open-ephys/onix-breakout/mechanical/case/components/cherryMX/Renderings/untitled.199.jpg

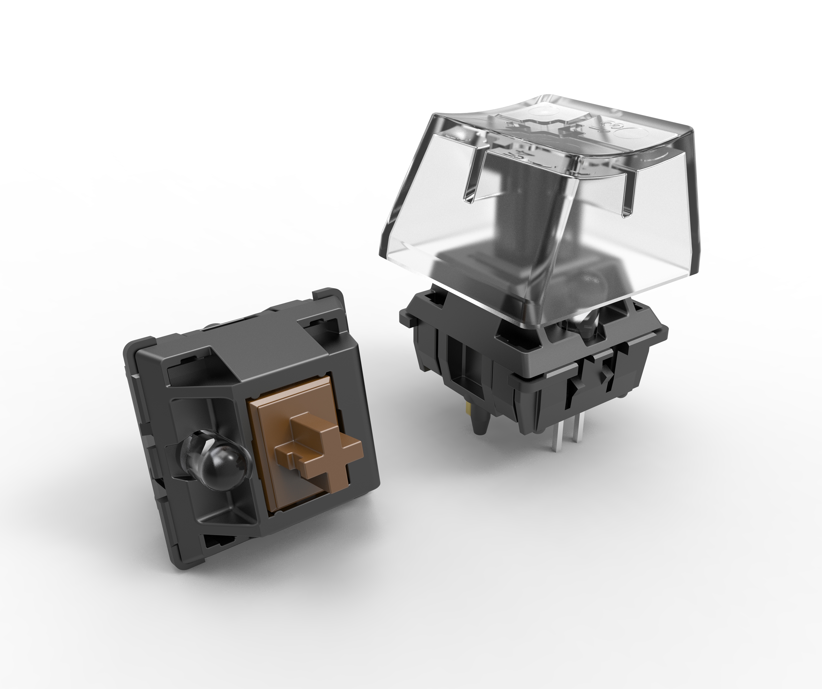
mechanical/case/components/cherryMX/Renderings/untitled.199.jpg
