open-ephys/onix-breakout/mechanical/case/components/cherryMX/Renderings/屏幕截图(25).jpg

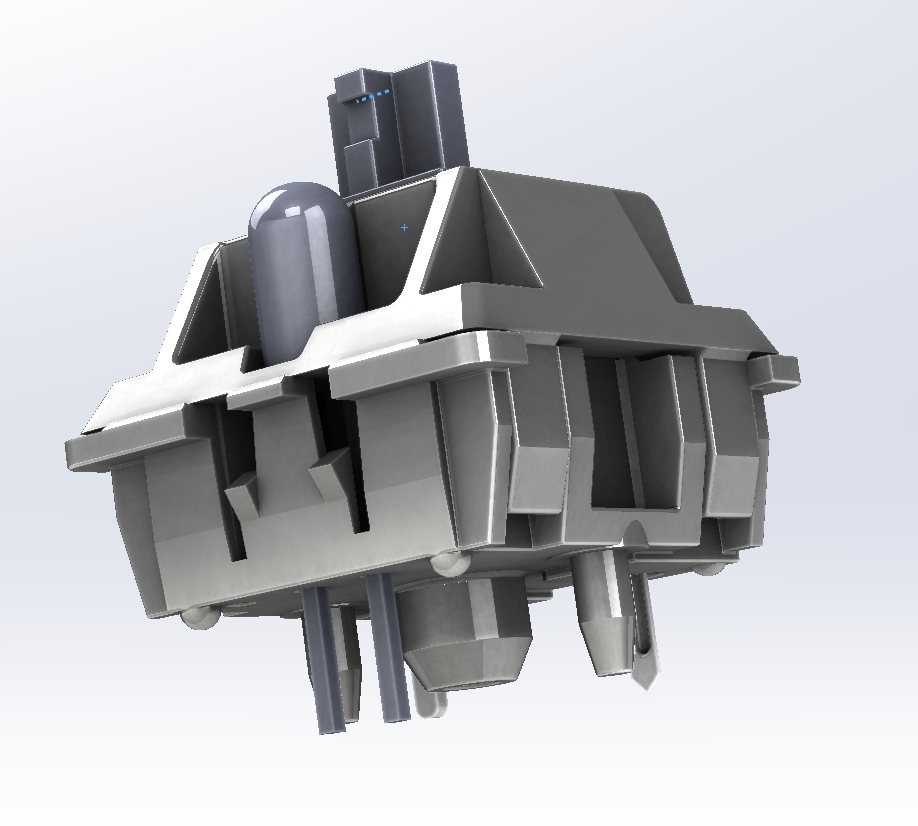
mechanical/case/components/cherryMX/Renderings/屏幕截图(25).jpg
