open-ephys/onix-breakout/mechanical/case/components/teensy/Renderings/Teensy_3_1 v12.png

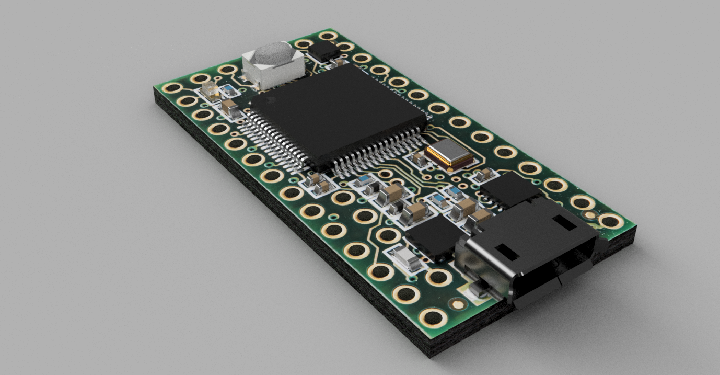
mechanical/case/components/teensy/Renderings/Teensy_3_1 v12.png
