open-ephys/onix-breakout/mechanical/case/components/cherryMX/MX轴 轴体 底部.SLDPRT

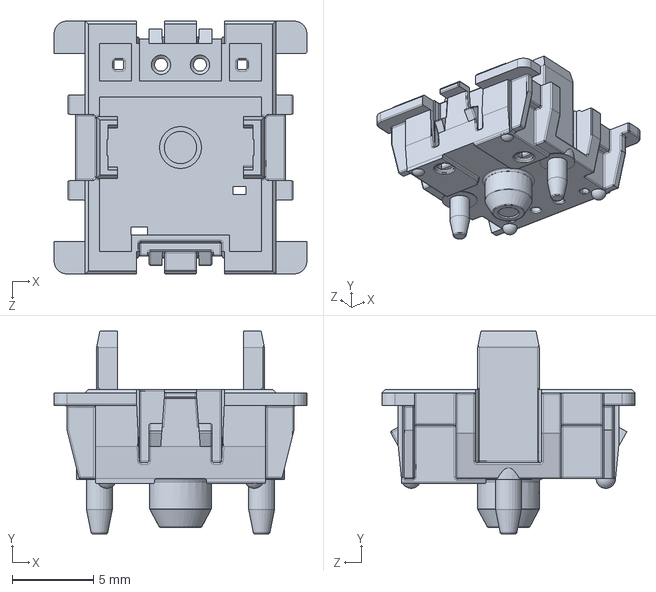
[picture p27: CAD file, 2019-09-01]
mechanical/case/components/cherryMX/MX轴 轴体 底部.SLDPRT
15.6 x 12.5 x 15.6 mm
