open-ephys/onix-breakout/mechanical/case/components/mmcx_through_hole.SLDPRT

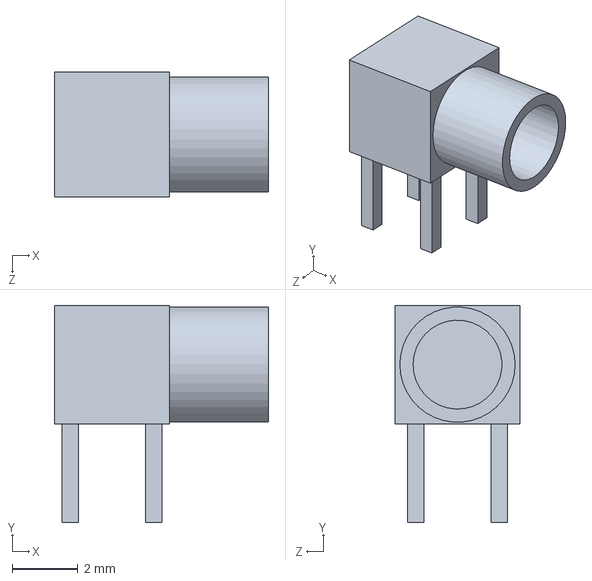
[picture p28: CAD file, 2019-12-28]
mechanical/case/components/mmcx_through_hole.SLDPRT
6.50 x 6.60 x 3.80 mm
