open-ephys/onix-breakout/mechanical/case/components/bnc_112538.SLDPRT

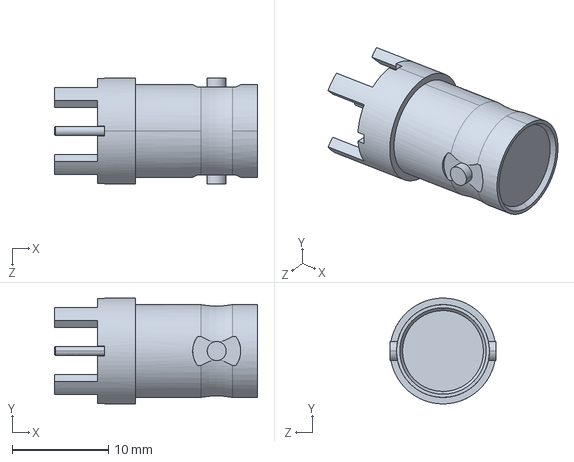
[picture p31: CAD file, 2019-12-28]
mechanical/case/components/bnc_112538.SLDPRT
21.1 x 11.0 x 11.0 mm
