open-ephys/onix-breakout/mechanical/case/components/cherryMX/MX 轴 轴体.SLDPRT

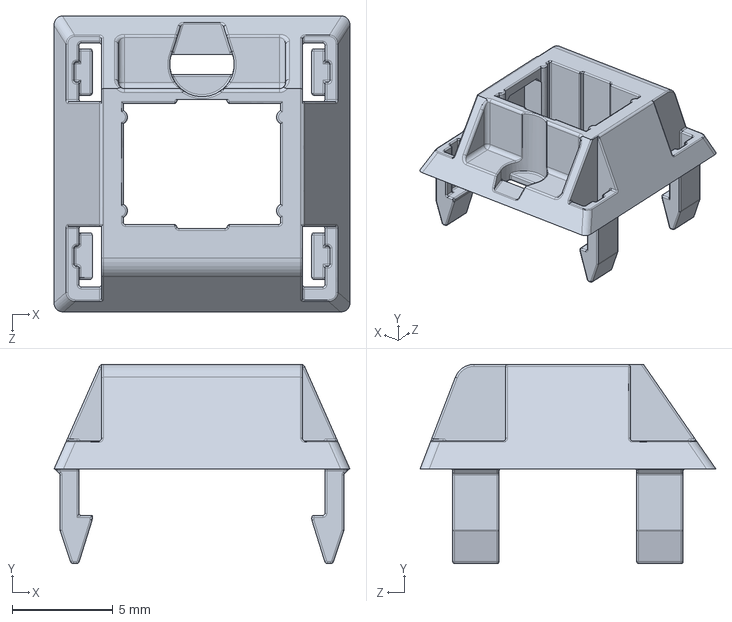
[picture p32: CAD file, 2019-09-01]
mechanical/case/components/cherryMX/MX 轴 轴体.SLDPRT
14.7 x 9.90 x 14.7 mm
