open-ephys/onix-breakout/mechanical/case/components/cherryMX/针脚.SLDPRT

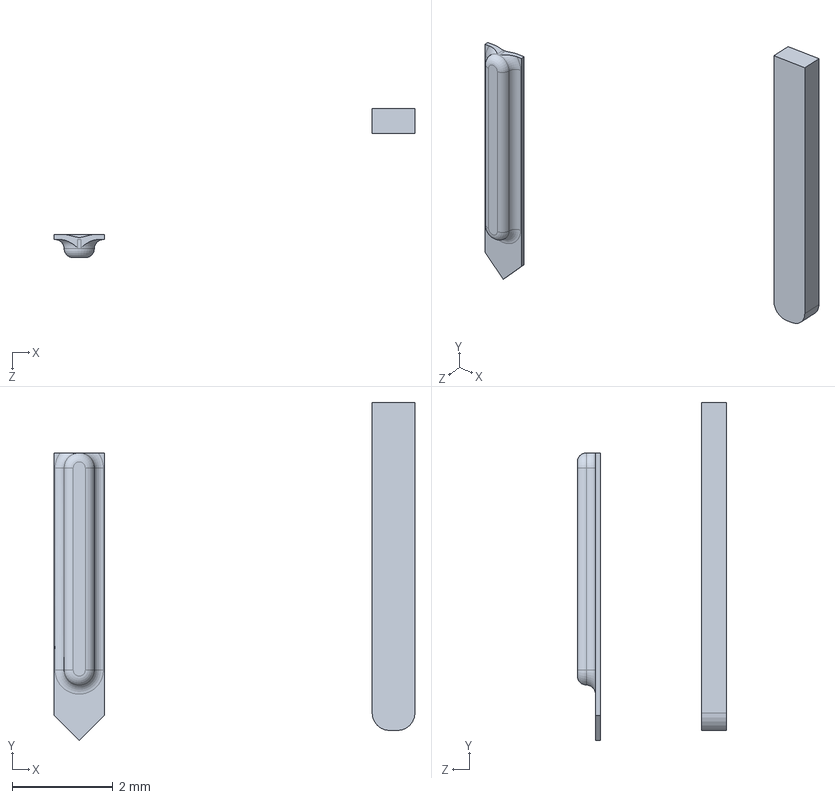
[picture p34: CAD file, 2019-09-01]
mechanical/case/components/cherryMX/针脚.SLDPRT
7.15 x 6.70 x 2.96 mm
