open-ephys/onix-breakout/mechanical/case/components/header_69168-x20.SLDPRT

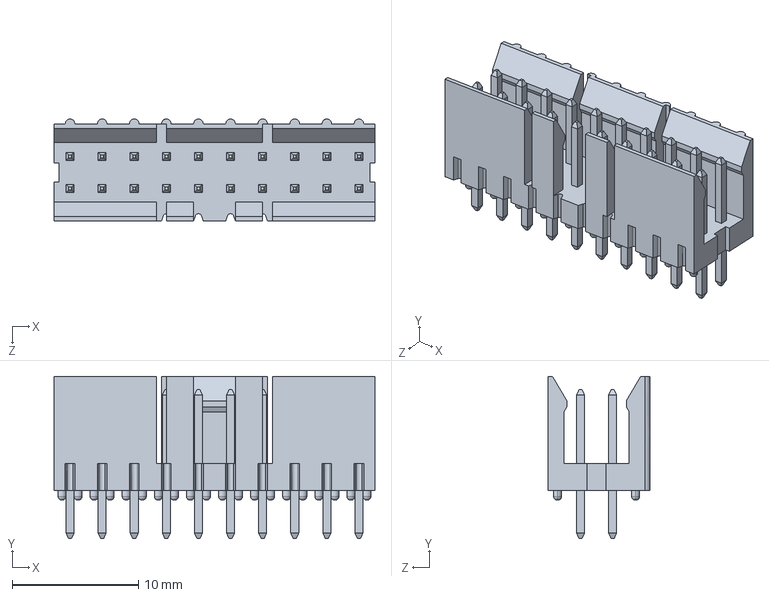
[picture p35: CAD file, 2019-12-28]
mechanical/case/components/header_69168-x20.SLDPRT
25.4 x 12.9 x 8.08 mm
