open-ephys/onix-breakout/mechanical/case/pcb_spacer_lasercut.SLDPRT

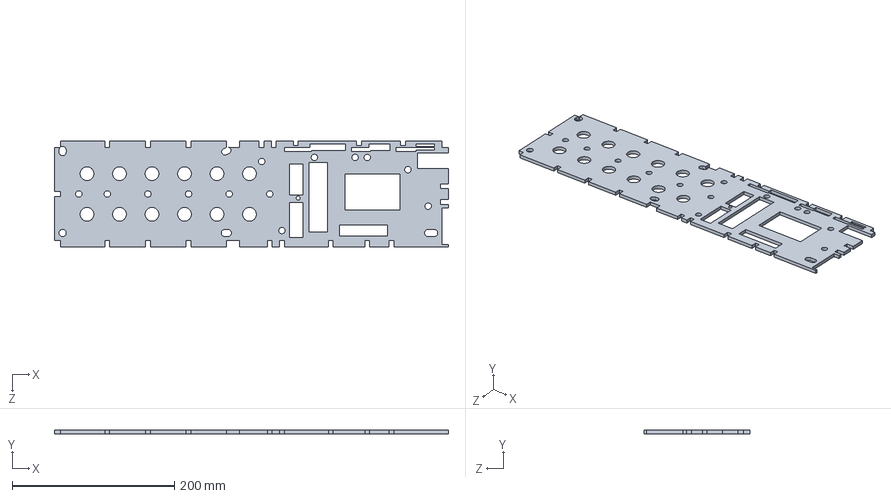
[picture p36: CAD file, 2021-03-16]
mechanical/case/pcb_spacer_lasercut.SLDPRT
485.0 x 4.50 x 130.0 mm
