open-ephys/onix-breakout/mechanical/case/pcb_bottom_waterjet.SLDPRT

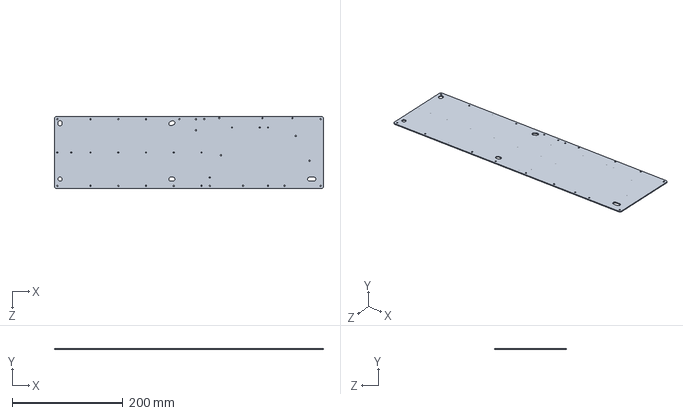
[picture p38: CAD file, 2021-03-16]
mechanical/case/pcb_bottom_waterjet.SLDPRT
485.0 x 1.50 x 130.0 mm
