open-ephys/onix-breakout/mechanical/case/components/cherryMX/MX 轴 按键.SLDPRT

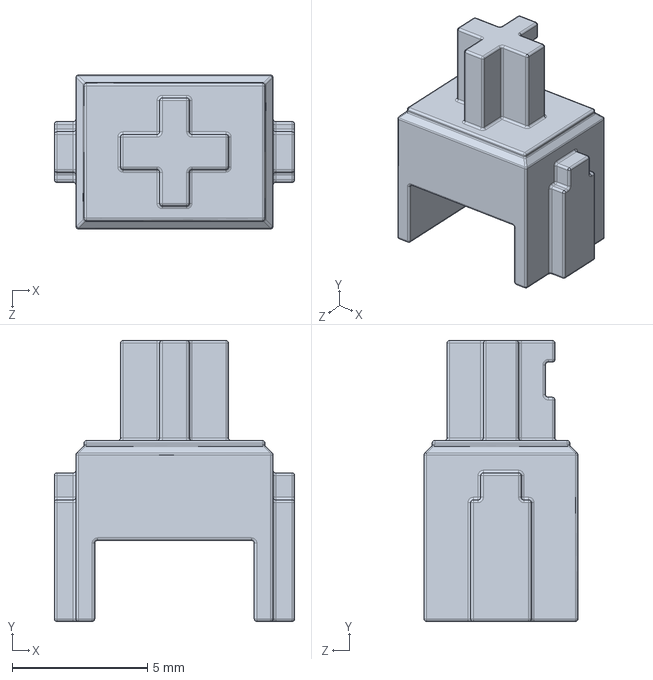
[picture p39: CAD file, 2019-09-01]
mechanical/case/components/cherryMX/MX 轴 按键.SLDPRT
8.90 x 10.4 x 5.70 mm
