open-ephys/onix-breakout/mechanical/case/pcb_bottom_waterjet_3mm_aluminum.DXF

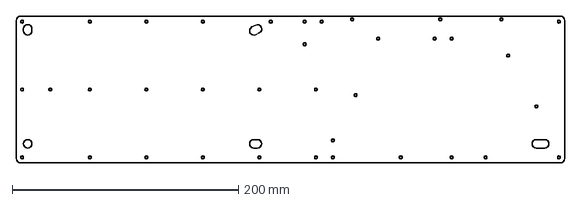
[picture p41: CAD file, 2021-03-16]
mechanical/case/pcb_bottom_waterjet_3mm_aluminum.DXF
485.0 x 130.0 mm
