open-ephys/onix-breakout/mechanical/case/breakout_case_pcb.SLDPRT

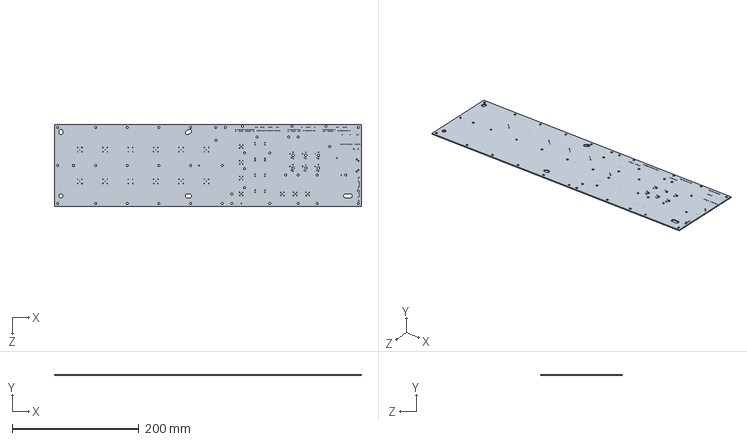
[picture p42: CAD file, 2020-09-03]
mechanical/case/breakout_case_pcb.SLDPRT
485.0 x 1.60 x 130.0 mm
