open-ephys/onix-breakout/mechanical/case/components/sma_small_c-5-1814832-1-b-3d.stp

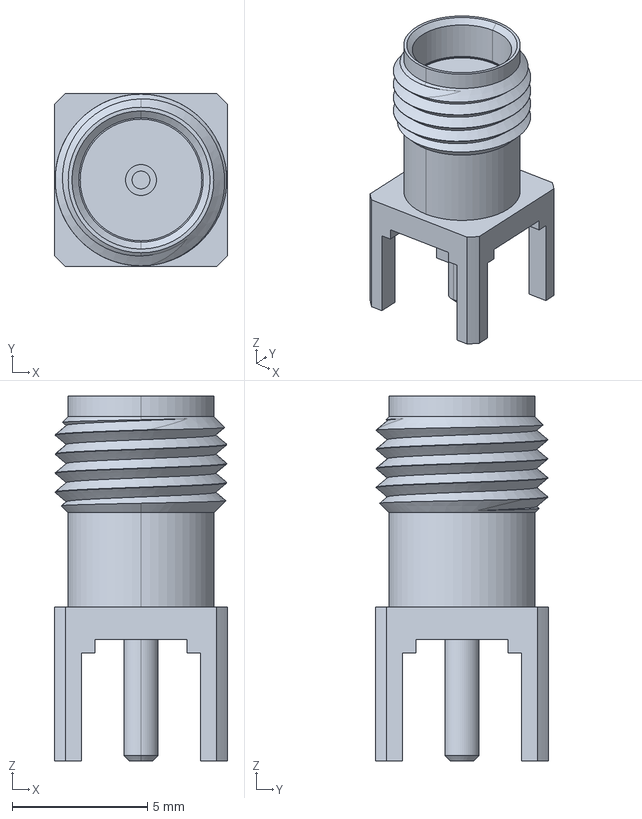
[picture p44: CAD file, 2019-09-01]
mechanical/case/components/sma_small_c-5-1814832-1-b-3d.stp
6.40 x 6.40 x 13.5 mm
