open-ephys/onix-breakout/mechanical/case/WP154A4SEJ3VBDZGW-CA_rgb-led.SLDPRT

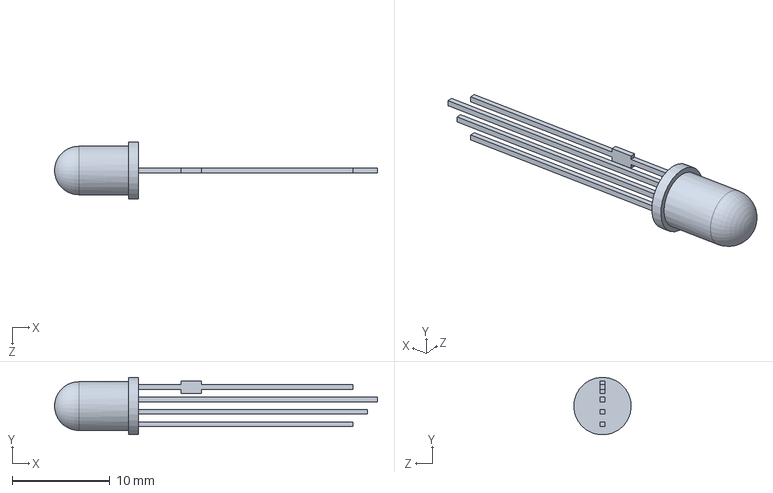
[picture p47: CAD file, 2020-05-01]
mechanical/case/WP154A4SEJ3VBDZGW-CA_rgb-led.SLDPRT
33.1 x 5.88 x 5.89 mm
