open-ephys/onix-breakout/gateware/breakout_to_host.v

// This module transmits data through 2 serialized lines transmitting 16-bits
// words using 8b/10b, plus a control code, for a total of 30 coded bits at 60MHz
// This results in 2MHz per line. However, digital inputs are sent in both lines, sampled
// at an offset, so digital input bandwidth can be 4MHz, while button and power status is 2MHz
//
// Data words are:
// D0: [din7, ..., din1, din0, X, X, but5, ..., but1, but0]
// D1: [din7, ..., din1, din0, X, X, X, X, pow3, pow2, pow1, pow0]

`include "lvds_8b10b_send.v"

module breakout_to_host (

    input   wire        i_clk,

    // Parallel inputs
    input   wire [7:0]  i_port,
    input   wire [5:0]  i_button,
    input   wire [3:0]  i_link_pow,

    input   wire        i_harp,

    // Serial outputs
    output  wire        o_clk_s,
    output  wire        o_d0_s,
    output  wire        o_d1_s
);

wire d0_s, d1_s;
wire d0_reset, d1_reset;
reg [15:0] d0_data;
reg [15:0] d1_data;
wire d0_data_rq, d1_data_rq;
wire harp_sync;
reg harp_sync_reg = 1'b1;

// Reset sequence. Since each transmission takes 30 cycles, we can sample the
// digital inputs at twice the speed by starting both lines with a 15 cycle
// offset.
reg [4:0] count;
initial begin
    count <= 5'b0;
end

// Count up to 20
always @(posedge i_clk) begin
    if (count < 5'd20) begin
        count <= count + 1'b1;
    end
end

// Start the first line at 5 cycles, to give time to other parts to start
// producing data
assign d0_reset = (count < 5'd5) ? 1'b1 : 1'b0;

// Start the second line 15 cycles after that
assign d1_reset = (count < 5'd20) ? 1'b1 : 1'b0;

lvds_8b10b_send # (
    .NUM_BYTES(2)
) d0 (
    .i_clk(i_clk),
    .i_reset(d0_reset),
    .i_data(d0_data),
    .o_data_read(d0_data_rq),
    .o_serial(d0_s)
);

lvds_8b10b_send # (
    .NUM_BYTES(2)
) d1 (
    .i_clk(i_clk),
    .i_reset(d1_reset),
    .i_data(d1_data),
    .o_data_read(d1_data_rq),
    .o_serial(d1_s)
);

// Port sampling
always @(posedge i_clk) begin
    if (d0_data_rq) begin
        d0_data <= {i_port, harp_sync_reg, 1'b0, i_button};
    end

    if (d1_data_rq) begin
        d1_data <= {i_port, harp_sync_reg, 3'b000, i_link_pow};
    end
end

// Simple, unregistered output buffers
SB_IO # (
    .PIN_TYPE(6'b011000),
    .IO_STANDARD("SB_LVCMOS")
) clk_out (
    .PACKAGE_PIN(o_clk_s),
    .D_OUT_0(i_clk)
);

SB_IO # (
    .PIN_TYPE(6'b011000),
    .IO_STANDARD("SB_LVCMOS")
) d0_out (
    .PACKAGE_PIN(o_d0_s),
    .D_OUT_0(d0_s)
);

SB_IO # (
    .PIN_TYPE(6'b011000),
    .IO_STANDARD("SB_LVCMOS")
) d1_out (
    .PACKAGE_PIN(o_d1_s),
    .D_OUT_0(d1_s)
);

//harp registered input

SB_IO # (
    .PIN_TYPE(6'b 0000_00),
    .PULLUP(1'b1)
) din7 (
    .PACKAGE_PIN(i_harp),
    .D_IN_0(harp_sync),
    .CLOCK_ENABLE(1'b1),
    .INPUT_CLK(i_clk)
);

always @(posedge i_clk) begin
    harp_sync_reg <= harp_sync;
end

endmodule
